Wilfred-Mason/uMAMA/CAD/VISION_PUMP_ASSEMBLY/CAMERA_MOUNT_L.STL

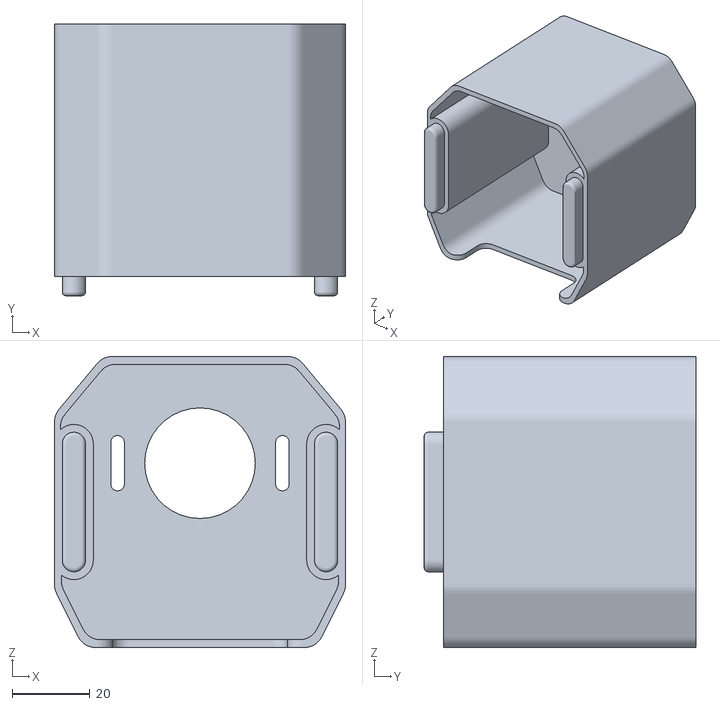
[picture p28: CAD file, 2023-06-23]
CAD/VISION_PUMP_ASSEMBLY/CAMERA_MOUNT_L.STL
75.0 x 70.0 x 75.0
