Wilfred-Mason/uMAMA/CAD/MELT_CUP_ASSEMBLY/Arm_Final.SLDPRT

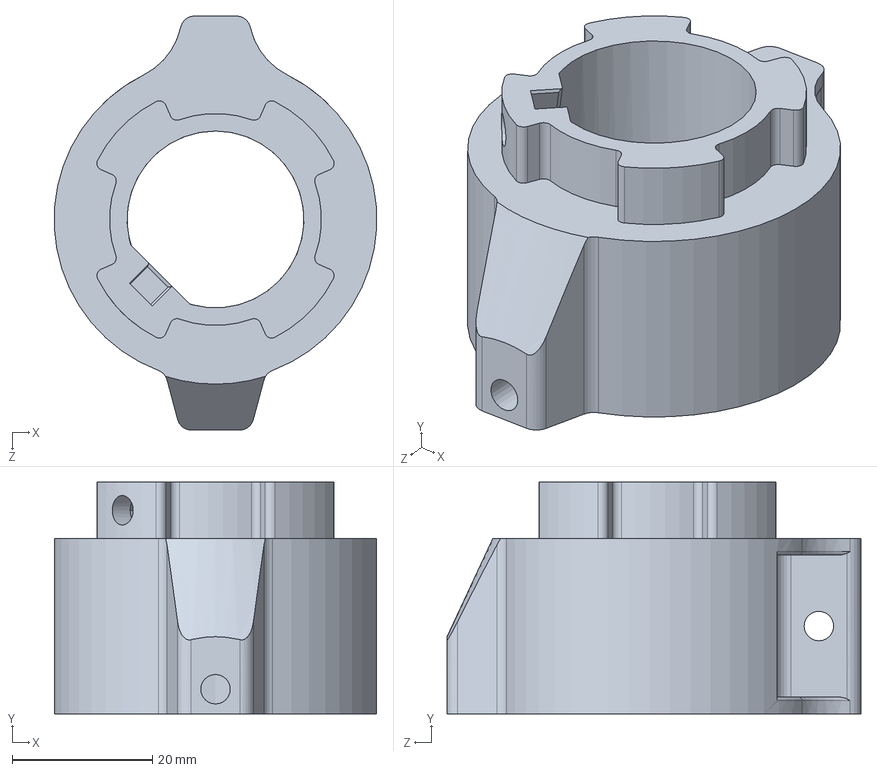
[picture p29: CAD file, 2023-12-01]
CAD/MELT_CUP_ASSEMBLY/Arm_Final.SLDPRT
45.9 x 33.0 x 59.0 mm
