Wilfred-Mason/uMAMA/CAD/VISION_PUMP_ASSEMBLY/LED_CASE_TOP.STL

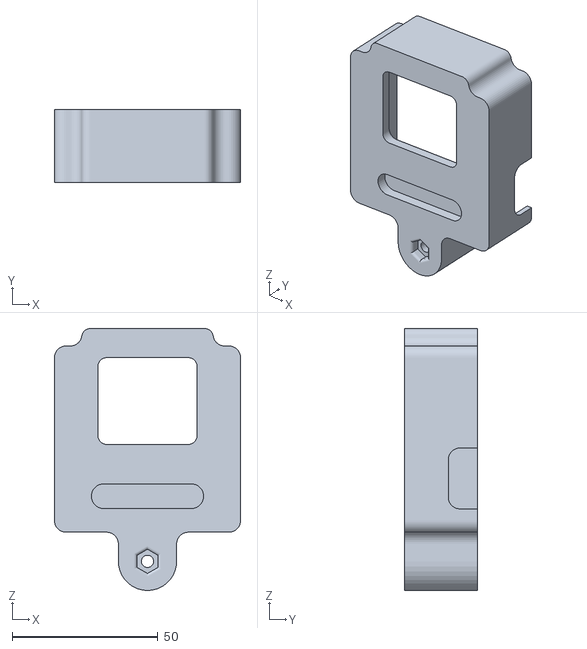
[picture p30: CAD file, 2023-06-23]
CAD/VISION_PUMP_ASSEMBLY/LED_CASE_TOP.STL
63.9 x 25.0 x 89.9
