Wilfred-Mason/uMAMA/CAD/MELT_CUP_ASSEMBLY/Electronics_Mount_Final.SLDPRT

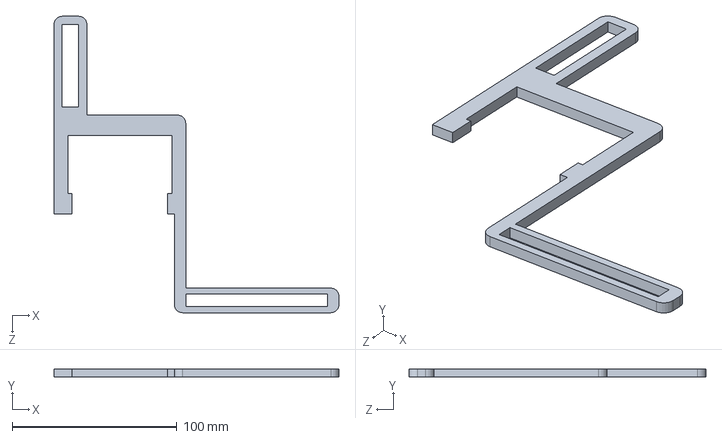
[picture p31: CAD file, 2023-12-01]
CAD/MELT_CUP_ASSEMBLY/Electronics_Mount_Final.SLDPRT
173.0 x 5.00 x 180.0 mm
