Wilfred-Mason/uMAMA/CAD/VISION_PUMP_ASSEMBLY/CAMERA_MOUNT_M.STL

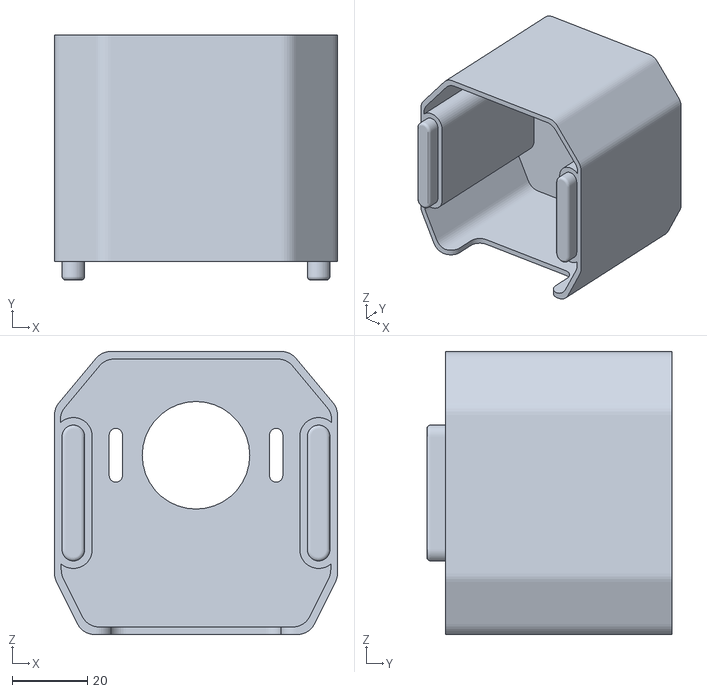
[picture p32: CAD file, 2023-06-23]
CAD/VISION_PUMP_ASSEMBLY/CAMERA_MOUNT_M.STL
75.0 x 65.0 x 75.0
