Wilfred-Mason/uMAMA/CAD/MELT_CUP_ASSEMBLY/Connector_Final.SLDPRT

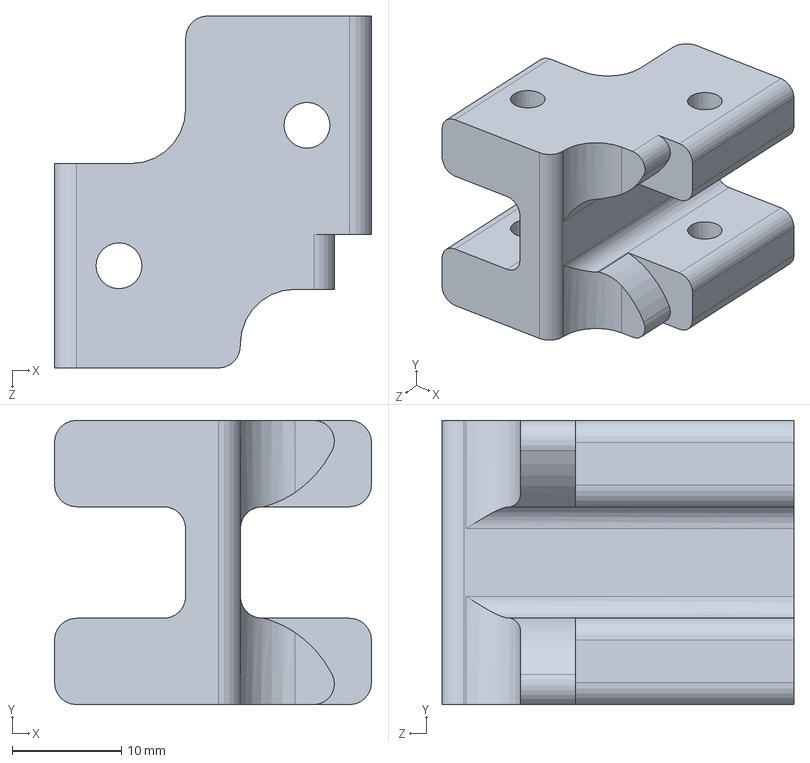
[picture p33: CAD file, 2023-12-01]
CAD/MELT_CUP_ASSEMBLY/Connector_Final.SLDPRT
29.0 x 26.0 x 32.2 mm
