Wilfred-Mason/uMAMA/CAD/VISION_PUMP_ASSEMBLY/LEG.STL

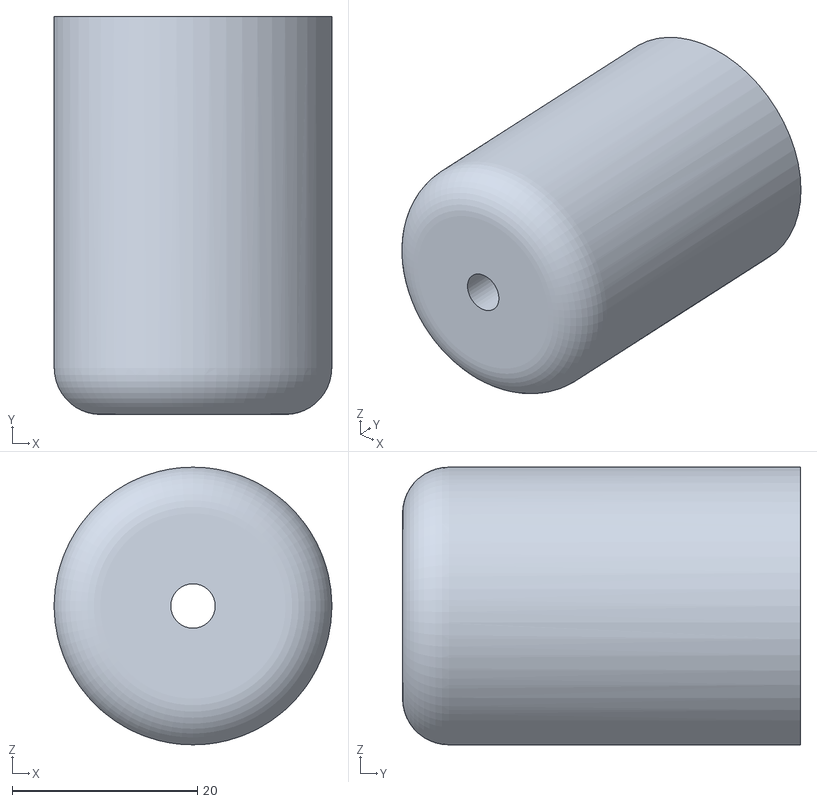
[picture p34: CAD file, 2023-06-23]
CAD/VISION_PUMP_ASSEMBLY/LEG.STL
30.0 x 43.0 x 30.0
