Wilfred-Mason/uMAMA/CAD/MELT_CUP_ASSEMBLY/Wire_Case_2.SLDPRT

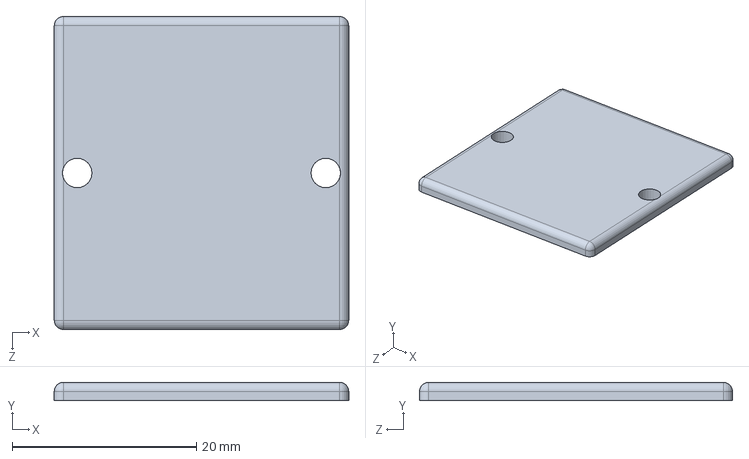
[picture p35: CAD file, 2023-12-01]
CAD/MELT_CUP_ASSEMBLY/Wire_Case_2.SLDPRT
32.0 x 2.00 x 34.0 mm
