Wilfred-Mason/uMAMA/CAD/VISION_PUMP_ASSEMBLY/LED_CASE_BOTTOM.STL

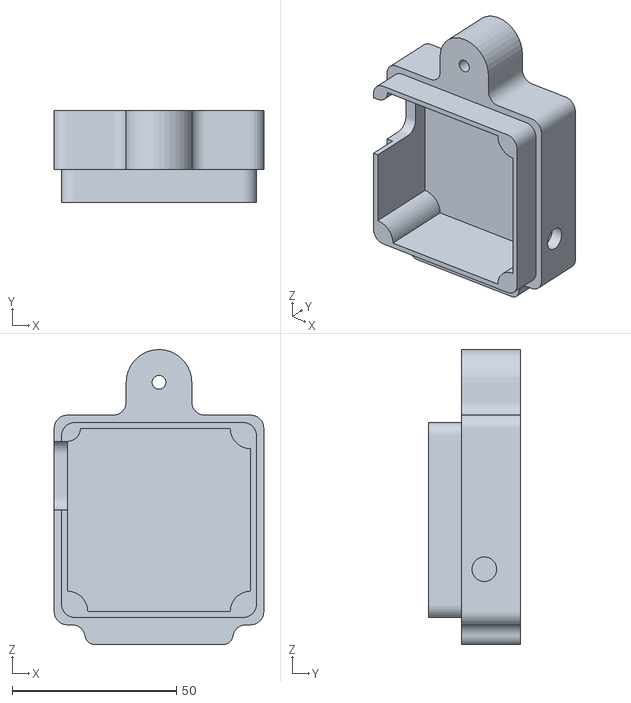
[picture p36: CAD file, 2023-06-23]
CAD/VISION_PUMP_ASSEMBLY/LED_CASE_BOTTOM.STL
63.9 x 28.0 x 89.9
