Wilfred-Mason/uMAMA/CAD/MELT_CUP_ASSEMBLY/Wire_Case_Large.SLDPRT

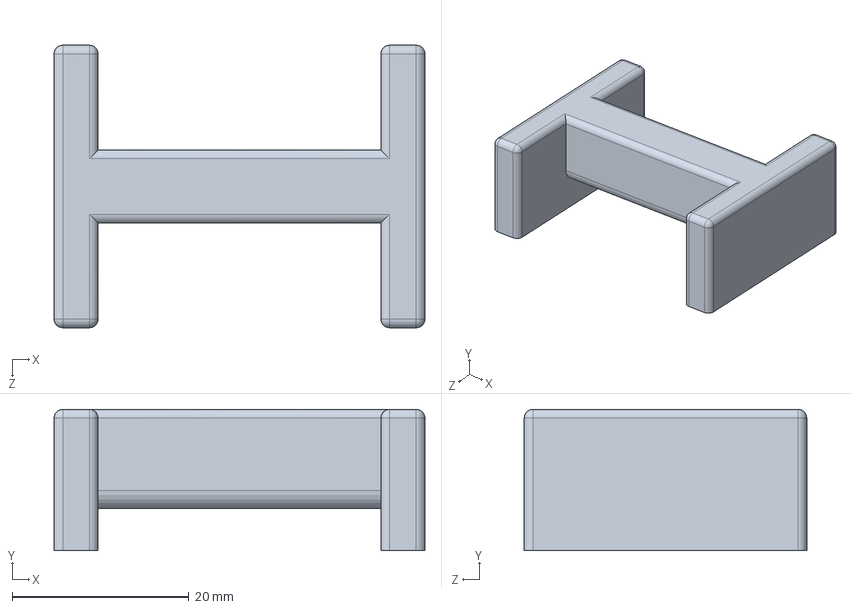
[picture p37: CAD file, 2023-12-01]
CAD/MELT_CUP_ASSEMBLY/Wire_Case_Large.SLDPRT
42.0 x 16.0 x 32.0 mm
