Wilfred-Mason/uMAMA/CAD/VISION_PUMP_ASSEMBLY/CAMERA_MOUNT_XL.STL

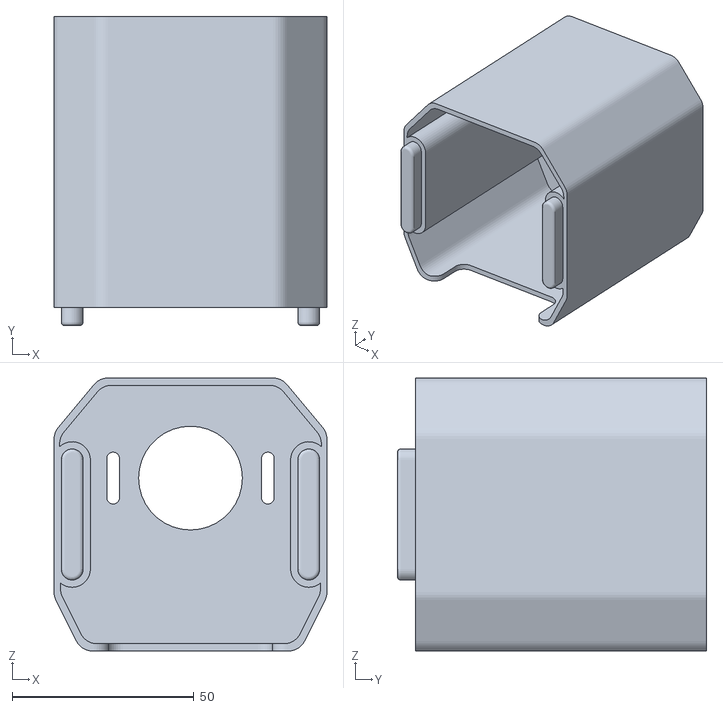
[picture p38: CAD file, 2023-06-23]
CAD/VISION_PUMP_ASSEMBLY/CAMERA_MOUNT_XL.STL
75.0 x 85.0 x 75.0
