Wilfred-Mason/uMAMA/CAD/MELT_CUP_ASSEMBLY/Cap_Final_Large.SLDPRT

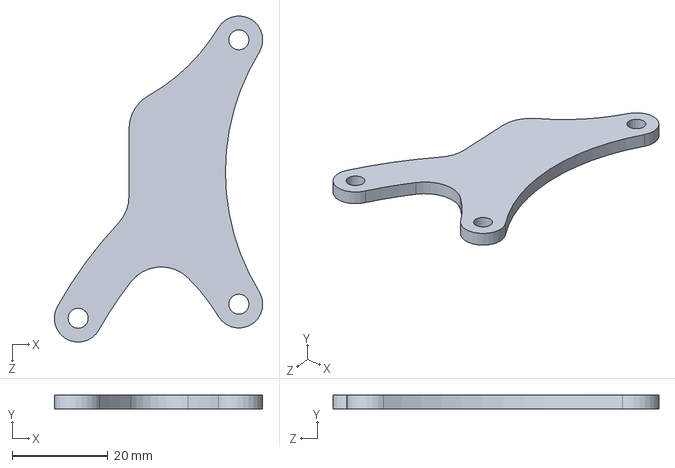
[picture p39: CAD file, 2023-12-01]
CAD/MELT_CUP_ASSEMBLY/Cap_Final_Large.SLDPRT
43.6 x 3.00 x 68.2 mm
