Wilfred-Mason/uMAMA/CAD/VISION_PUMP_ASSEMBLY/CAMERA_HOLDER.STL

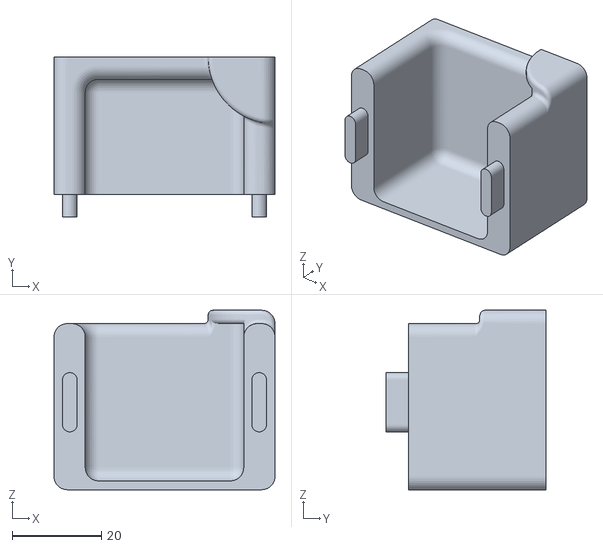
[picture p40: CAD file, 2023-06-23]
CAD/VISION_PUMP_ASSEMBLY/CAMERA_HOLDER.STL
49.6 x 35.9 x 40.3
