Wilfred-Mason/uMAMA/CAD/MELT_CUP_ASSEMBLY/Cap_Final.SLDPRT

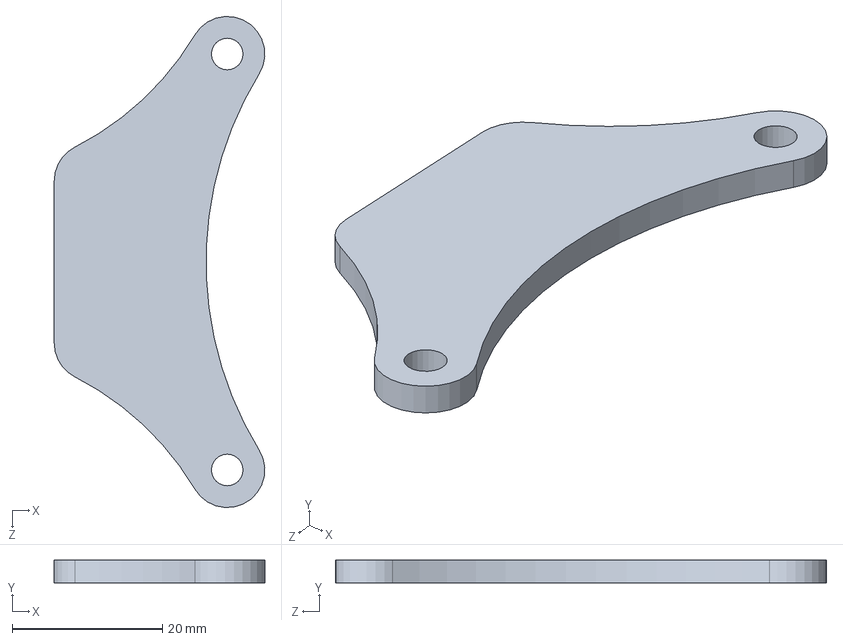
[picture p41: CAD file, 2023-12-01]
CAD/MELT_CUP_ASSEMBLY/Cap_Final.SLDPRT
28.0 x 3.00 x 65.3 mm
