Wilfred-Mason/uMAMA/CAD/VISION_PUMP_ASSEMBLY/PUMP_MOUNT.STL

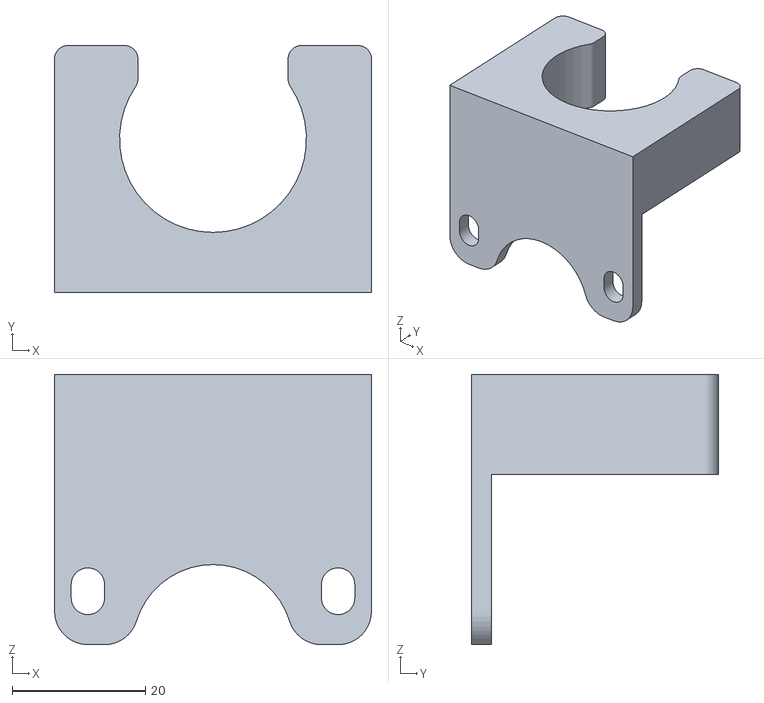
[picture p42: CAD file, 2023-06-23]
CAD/VISION_PUMP_ASSEMBLY/PUMP_MOUNT.STL
47.5 x 37.0 x 40.5
