Wilfred-Mason/uMAMA/CAD/MELT_CUP_ASSEMBLY/Cup_Final.SLDPRT

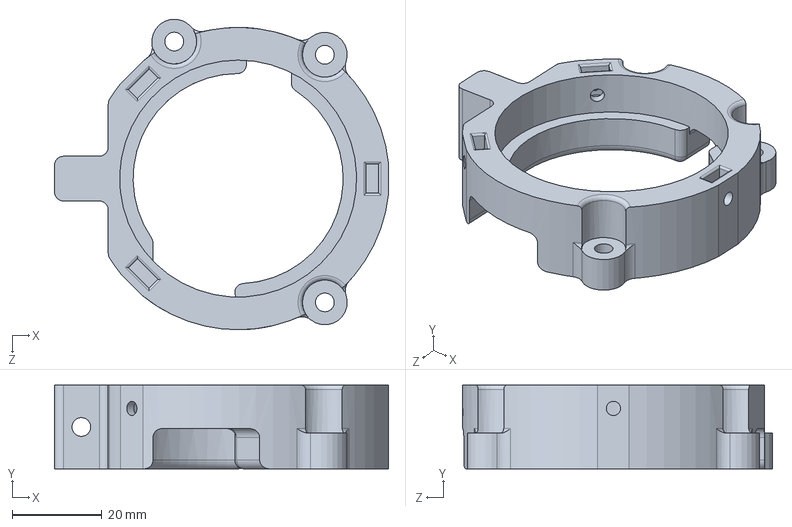
[picture p43: CAD file, 2023-12-01]
CAD/MELT_CUP_ASSEMBLY/Cup_Final.SLDPRT
74.6 x 18.7 x 69.3 mm
