Wilfred-Mason/uMAMA/CAD/VISION_PUMP_ASSEMBLY/NOTCH.STL

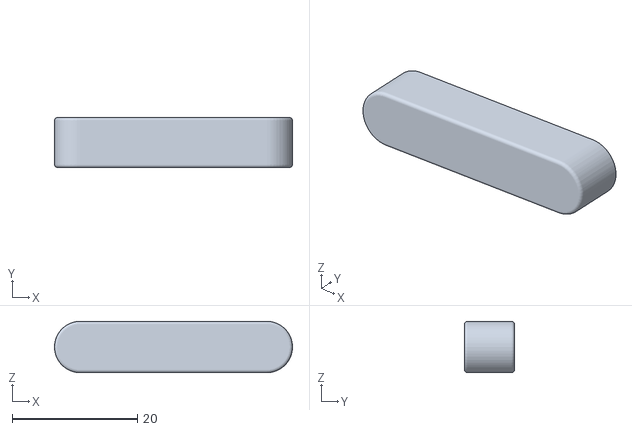
[picture p44: CAD file, 2023-06-23]
CAD/VISION_PUMP_ASSEMBLY/NOTCH.STL
38.0 x 8.00 x 8.20
