Wilfred-Mason/uMAMA/CAD/MELT_CUP_ASSEMBLY/Bearing_Ring_Final.SLDPRT

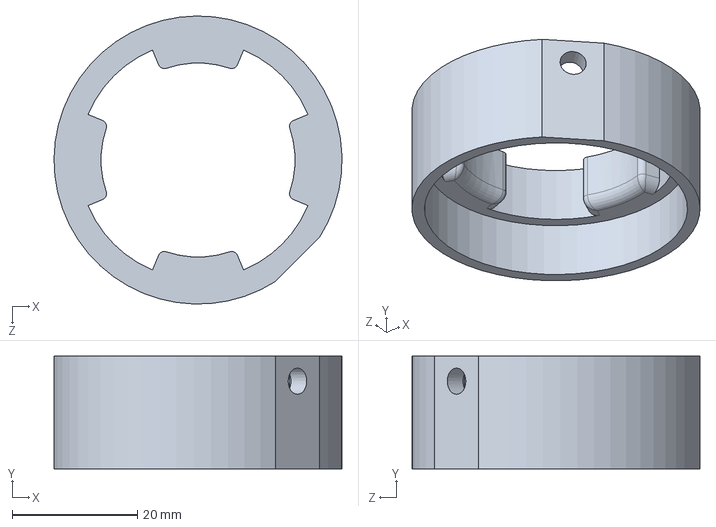
[picture p45: CAD file, 2023-12-01]
CAD/MELT_CUP_ASSEMBLY/Bearing_Ring_Final.SLDPRT
46.0 x 18.0 x 46.0 mm
