Wilfred-Mason/uMAMA/CAD/MELT_CUP_ASSEMBLY/Wire_Case_Large_2.SLDPRT

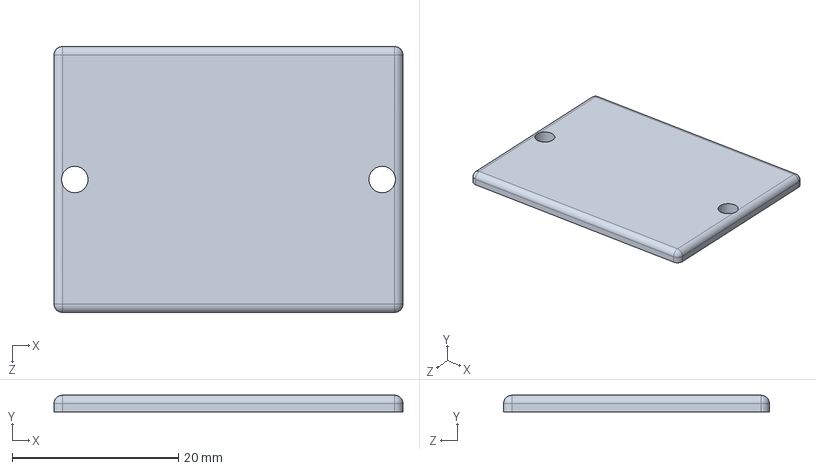
[picture p46: CAD file, 2023-12-01]
CAD/MELT_CUP_ASSEMBLY/Wire_Case_Large_2.SLDPRT
42.0 x 2.00 x 32.0 mm
