Wilfred-Mason/uMAMA/CAD/MELT_CUP_ASSEMBLY/Base_Final.SLDPRT

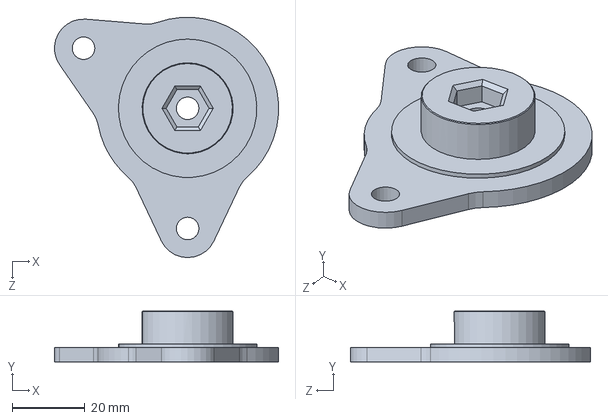
[picture p47: CAD file, 2023-12-01]
CAD/MELT_CUP_ASSEMBLY/Base_Final.SLDPRT
61.5 x 14.0 x 66.0 mm
